sstallion/usb-eeprom/usb.h

/******************************************************************************
 Software License Agreement:

 The software supplied herewith by Microchip Technology Incorporated
 (the "Company") for its PICmicro(r) Microcontroller is intended and
 supplied to you, the Company's customer, for use solely and
 exclusively on Microchip PICmicro Microcontroller products. The
 software is owned by the Company and/or its supplier, and is
 protected under applicable copyright laws. All rights are reserved.
 Any use in violation of the foregoing restrictions may subject the
 user to criminal sanctions under applicable laws, as well as to
 civil liability for the breach of the terms and conditions of this
 license.

 THIS SOFTWARE IS PROVIDED IN AN "AS IS" CONDITION. NO WARRANTIES,
 WHETHER EXPRESS, IMPLIED OR STATUTORY, INCLUDING, BUT NOT LIMITED
 TO, IMPLIED WARRANTIES OF MERCHANTABILITY AND FITNESS FOR A
 PARTICULAR PURPOSE APPLY TO THIS SOFTWARE. THE COMPANY SHALL NOT,
 IN ANY CIRCUMSTANCES, BE LIABLE FOR SPECIAL, INCIDENTAL OR
 CONSEQUENTIAL DAMAGES, FOR ANY REASON WHATSOEVER.
********************************************************************/

#ifndef _USB_H_
#define _USB_H_
//DOM-IGNORE-END

#if __XC16_VERSION__ == 1020
#error XC16 v1.20 is not compatible with this firmware, please use a later version of the XC16 compiler.
#endif

#if __XC8_VERSION == 1300
#error XC8 v1.30 is not compatible with this firmware, please use either XC8 v1.21 or a later version of the XC8 compiler.
#endif


// *****************************************************************************
// *****************************************************************************
// Section: All necessary USB Library headers
// *****************************************************************************
// *****************************************************************************

#include "usb_common.h"             // Common USB library definitions
#include "usb_ch9.h"                // USB device framework definitions

#if defined( USB_SUPPORT_DEVICE )
    #include "usb_device.h"         // USB Device abstraction layer interface
#endif

#if defined( USB_SUPPORT_HOST )
    #include "usb_host.h"           // USB Host abstraction layer interface
#endif

#if defined ( USB_SUPPORT_OTG )
    #include "usb_otg.h"
#endif

#include "usb_hal.h"                // Hardware Abstraction Layer interface

// *****************************************************************************
// *****************************************************************************
// Section: MCHPFSUSB Firmware Version
// *****************************************************************************
// *****************************************************************************

#define USB_MAJOR_VER   2       // Firmware version, major release number.
#define USB_MINOR_VER   10      // Firmware version, minor release number.
#define USB_DOT_VER     0       // Firmware version, dot release number.

#endif // _USB_H_
/*************************************************************************
 * EOF
 */
